Justwouter/workshop_bot/media/IMG_3868.JPG

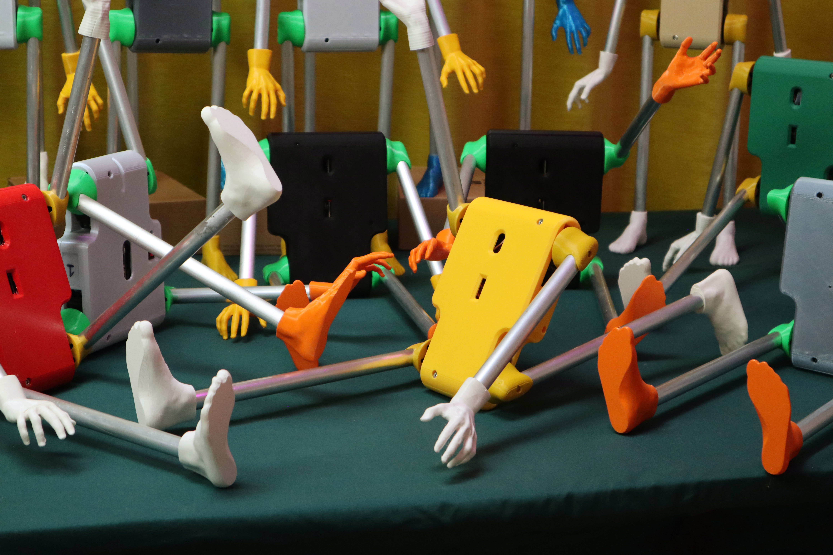
media/IMG_3868.JPG
