Justwouter/workshop_bot/media/IMG_4033.JPG

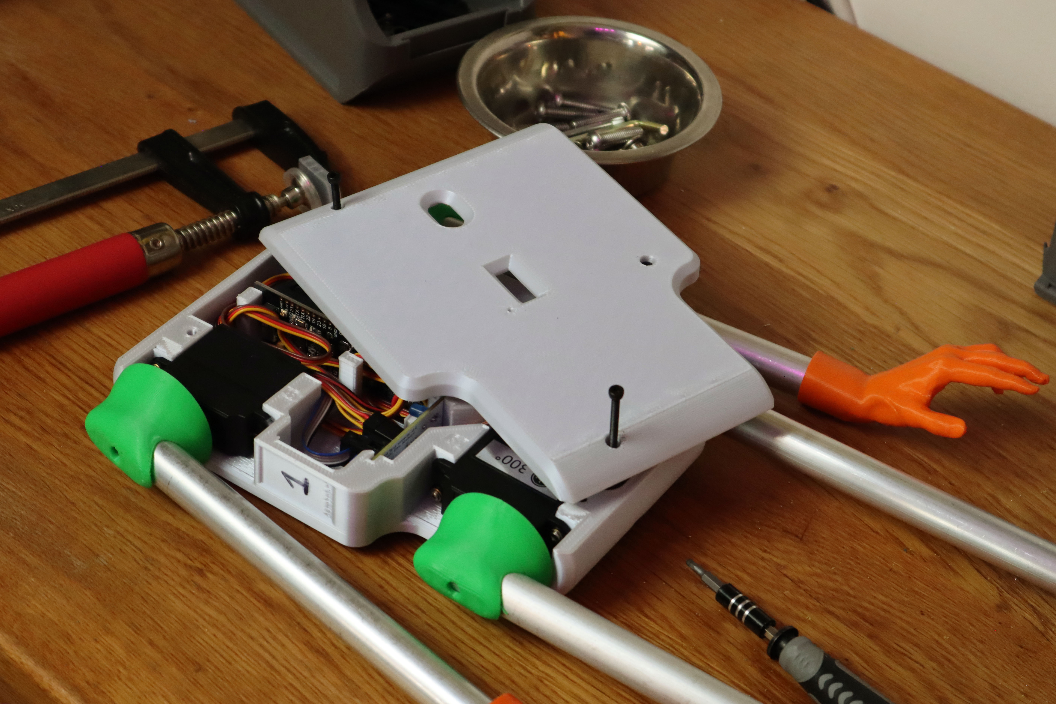
media/IMG_4033.JPG
